alberto-rota/Ender3-Upgrade/Printables/LED Bar Holder.stl

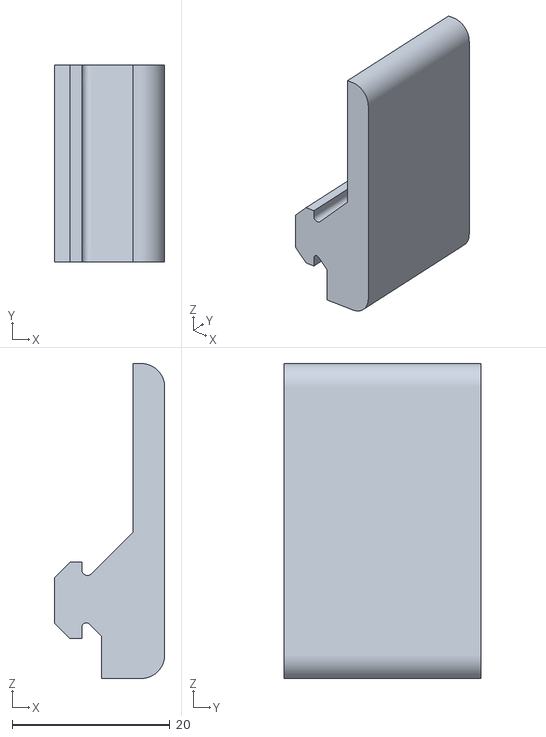
[picture p23: CAD file, 2023-01-06]
Printables/LED Bar Holder.stl
14.0 x 25.0 x 40.0
