alberto-rota/Ender3-Upgrade/Printables/Side_Drawers/Drawer_Bottom.stl

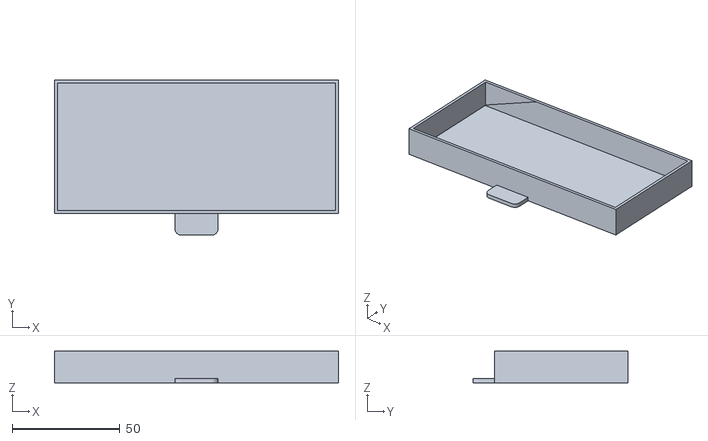
[picture p24: CAD file, 2023-03-15]
Printables/Side_Drawers/Drawer_Bottom.stl
131.5 x 72.0 x 14.8
