alberto-rota/Ender3-Upgrade/CAD/ExtrusionRail_20.dxf

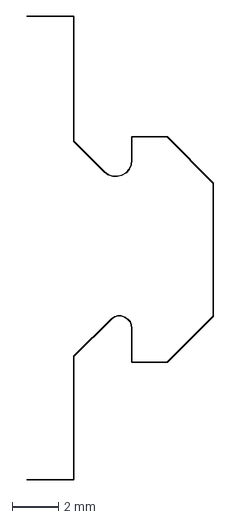
[picture p25: CAD file, 2023-01-06]
CAD/ExtrusionRail_20.dxf
8.05 x 20.0 mm
