alberto-rota/Ender3-Upgrade/CAD/LM2596 DC to DC Buck Converter 3 A/smd220uF.SLDPRT

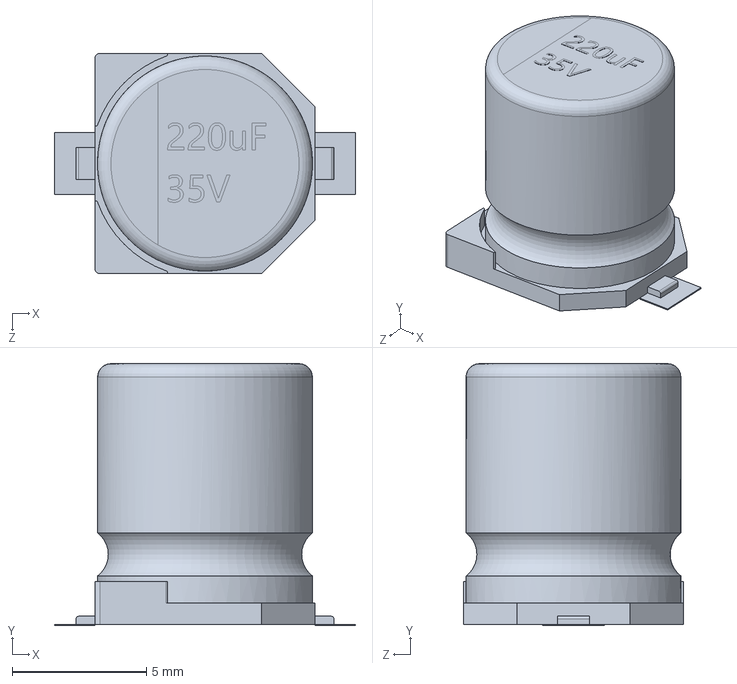
[picture p26: CAD file, 2023-01-05]
CAD/LM2596 DC to DC Buck Converter 3 A/smd220uF.SLDPRT
11.2 x 9.76 x 8.20 mm
