alberto-rota/Ender3-Upgrade/PCB/BuckConverter.dxf

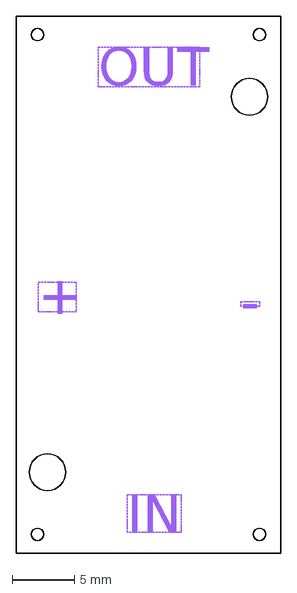
[picture p27: CAD file, 2023-01-05]
PCB/BuckConverter.dxf
IN
OUT
-
+
