alberto-rota/Ender3-Upgrade/Printables/Cablechain/cableChain_bedCorner_v2.stl

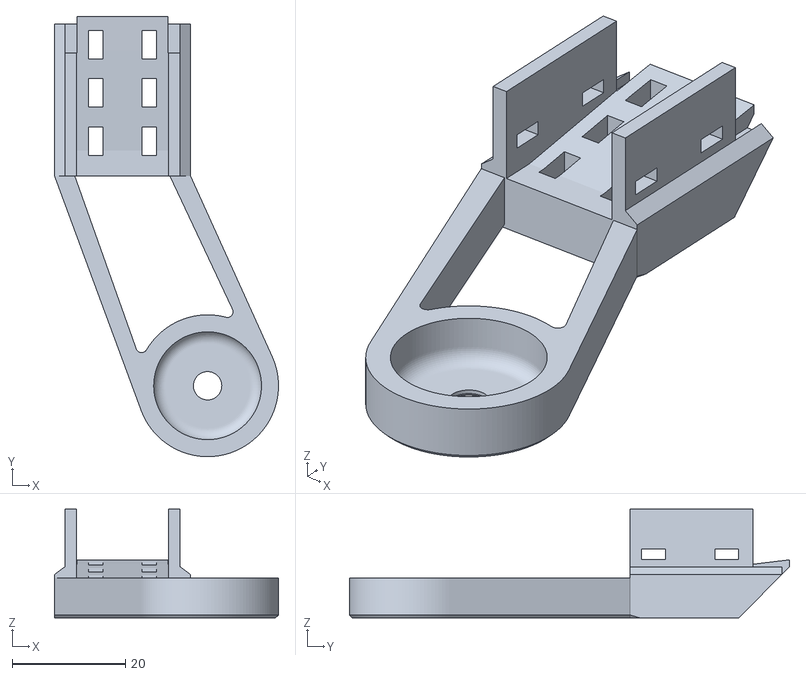
[picture p28: CAD file, 2023-03-15]
Printables/Cablechain/cableChain_bedCorner_v2.stl
39.5 x 77.6 x 19.2
