alberto-rota/Ender3-Upgrade/Printables/Camera Wire Clip.stl

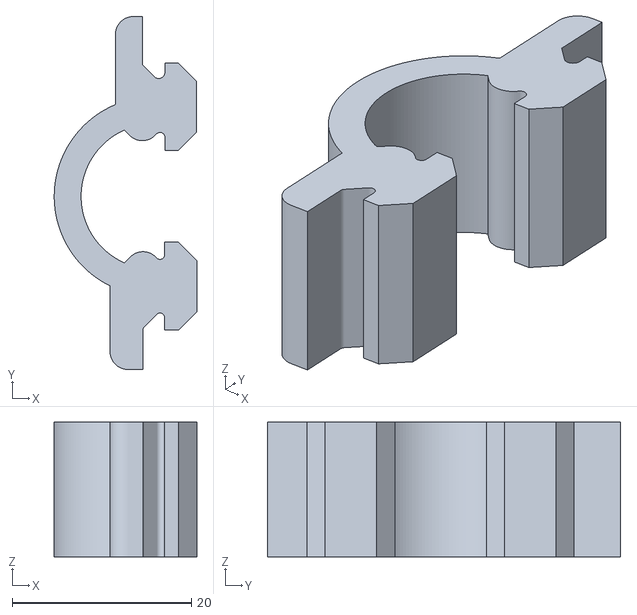
[picture p29: CAD file, 2023-01-06]
Printables/Camera Wire Clip.stl
15.9 x 39.4 x 15.0
