alberto-rota/Ender3-Upgrade/Printables/Front_Drawers/BOTTOM_DRAWER.stl

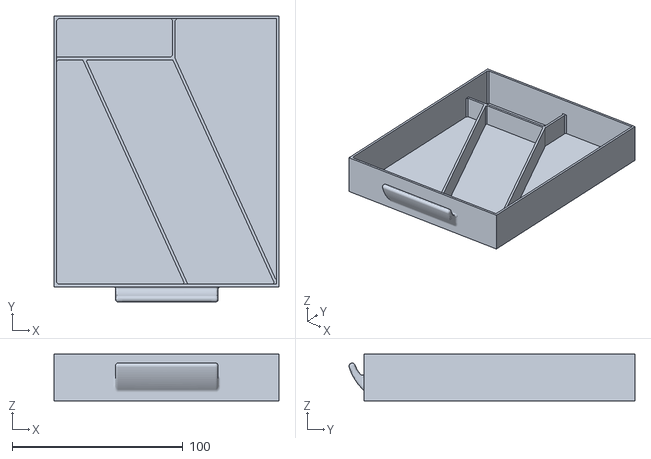
[picture p30: CAD file, 2023-03-15]
Printables/Front_Drawers/BOTTOM_DRAWER.stl
131.6 x 167.3 x 27.4
