alberto-rota/Ender3-Upgrade/Printables/Side_Drawers/Drawer_TopRight.stl

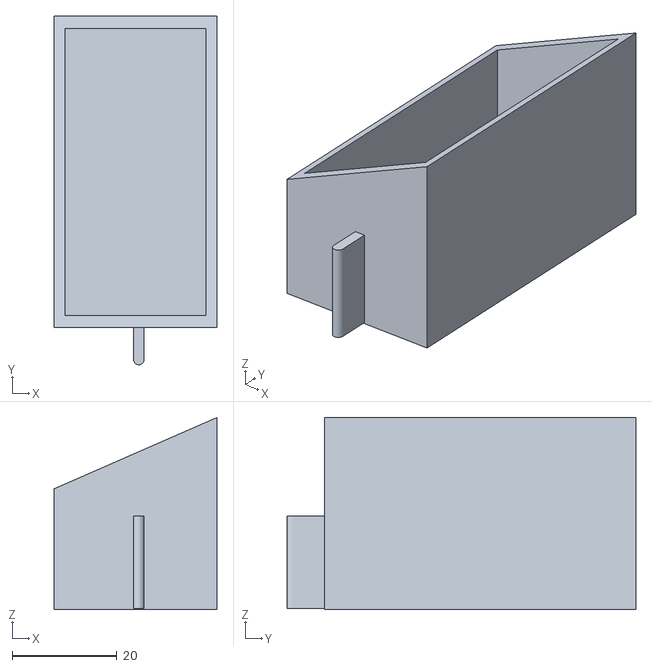
[picture p31: CAD file, 2023-03-15]
Printables/Side_Drawers/Drawer_TopRight.stl
31.0 x 66.4 x 36.6
