alberto-rota/Ender3-Upgrade/Printables/Cablechain/cableChain_40MountTop_v2.stl

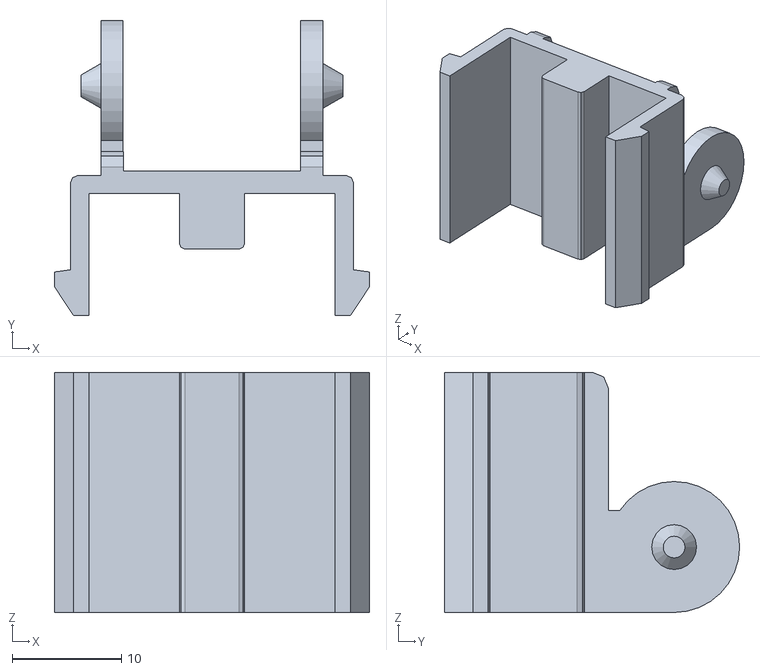
[picture p32: CAD file, 2023-03-15]
Printables/Cablechain/cableChain_40MountTop_v2.stl
28.9 x 27.1 x 22.0
