alberto-rota/Ender3-Upgrade/Printables/Side_Drawers/Drawer_Middle.stl

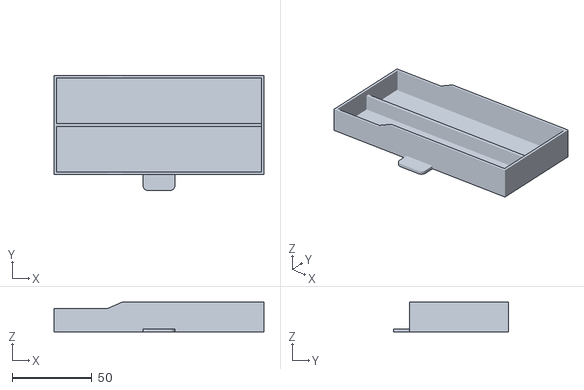
[picture p33: CAD file, 2023-03-15]
Printables/Side_Drawers/Drawer_Middle.stl
131.5 x 72.0 x 18.8
