alberto-rota/Ender3-Upgrade/CAD/LM2596 DC to DC Buck Converter 3 A/LM2596S.SLDPRT

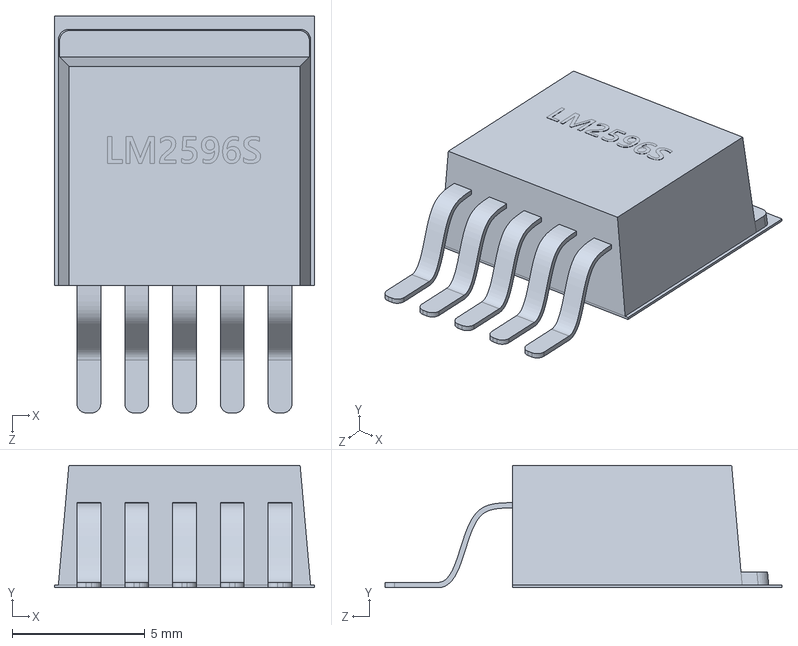
[picture p34: CAD file, 2023-01-05]
CAD/LM2596 DC to DC Buck Converter 3 A/LM2596S.SLDPRT
9.80 x 4.61 x 14.9 mm
