alberto-rota/Ender3-Upgrade/Printables/Cablechain/cableChain_Xend.stl

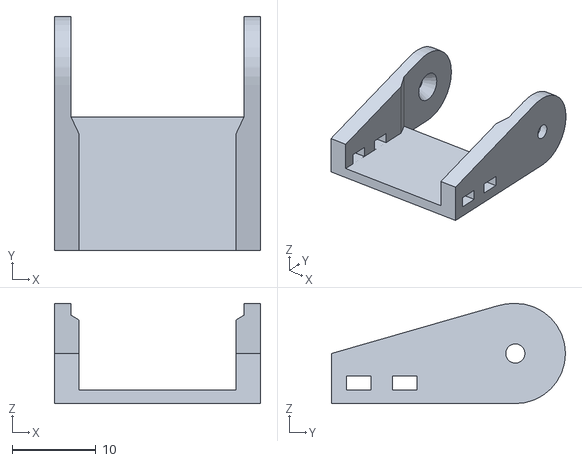
[picture p35: CAD file, 2023-03-15]
Printables/Cablechain/cableChain_Xend.stl
24.7 x 28.0 x 12.0
