alberto-rota/Ender3-Upgrade/Printables/Side_Drawers/Drawer_Holder.stl

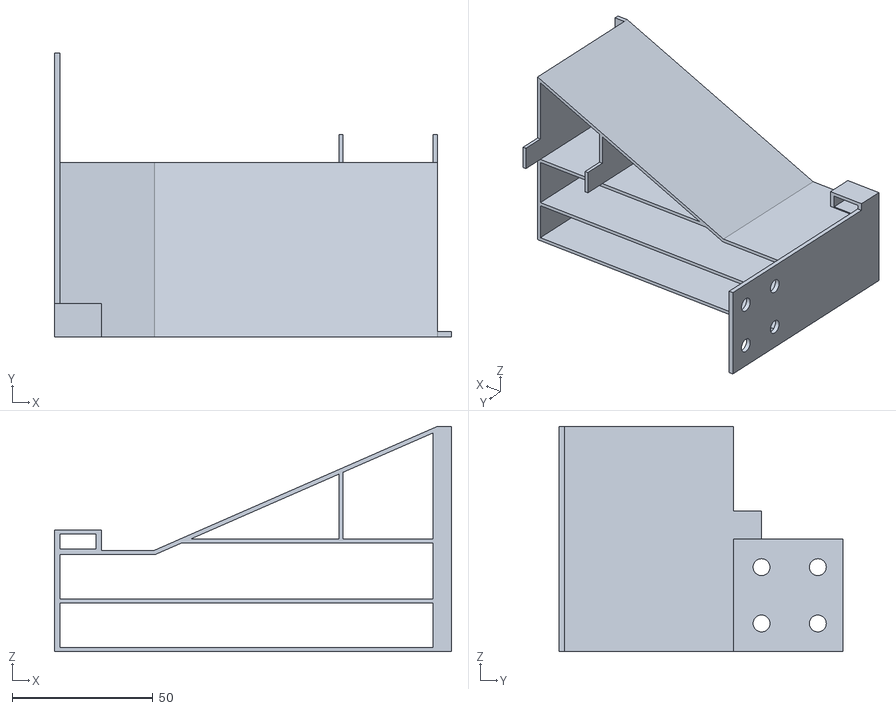
[picture p36: CAD file, 2023-03-15]
Printables/Side_Drawers/Drawer_Holder.stl
141.0 x 101.0 x 80.0
