alberto-rota/Ender3-Upgrade/CAD/LM2596 DC to DC Buck Converter 3 A/smbInductor470.SLDPRT

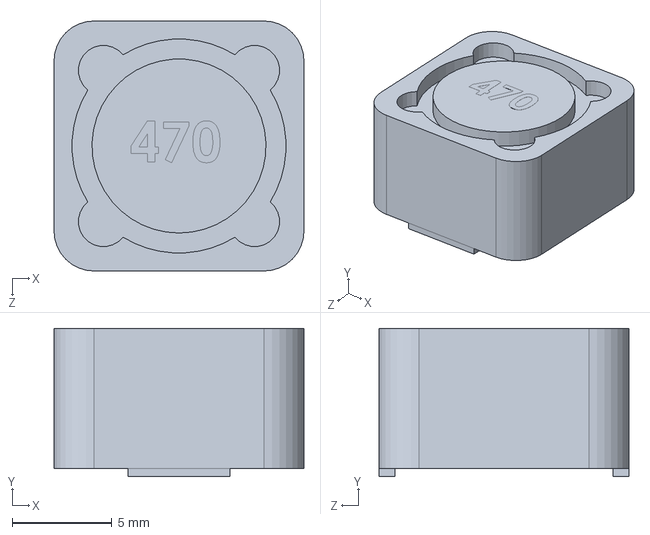
[picture p37: CAD file, 2023-01-05]
CAD/LM2596 DC to DC Buck Converter 3 A/smbInductor470.SLDPRT
12.5 x 7.41 x 12.5 mm
