alberto-rota/Ender3-Upgrade/CAD/LM2596 DC to DC Buck Converter 3 A/smdLED.SLDPRT

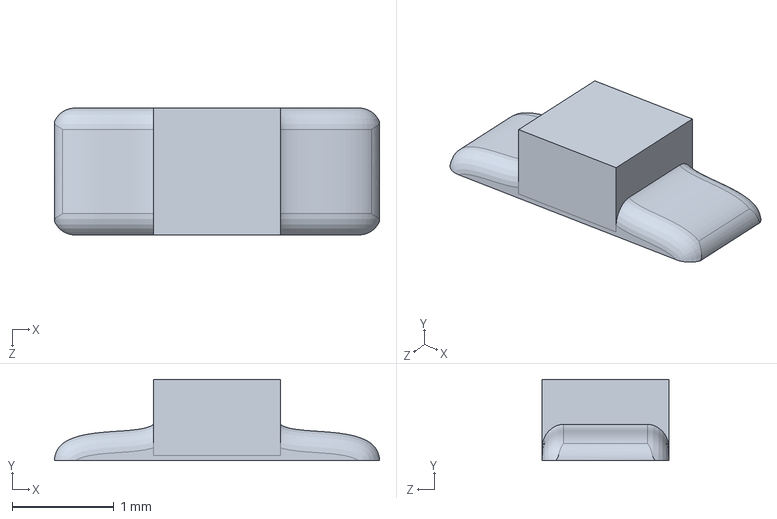
[picture p38: CAD file, 2023-01-05]
CAD/LM2596 DC to DC Buck Converter 3 A/smdLED.SLDPRT
3.20 x 0.8 x 1.25 mm
