alberto-rota/Ender3-Upgrade/Printables/Cablechain/cableChain_bedCornerCover_v2.stl

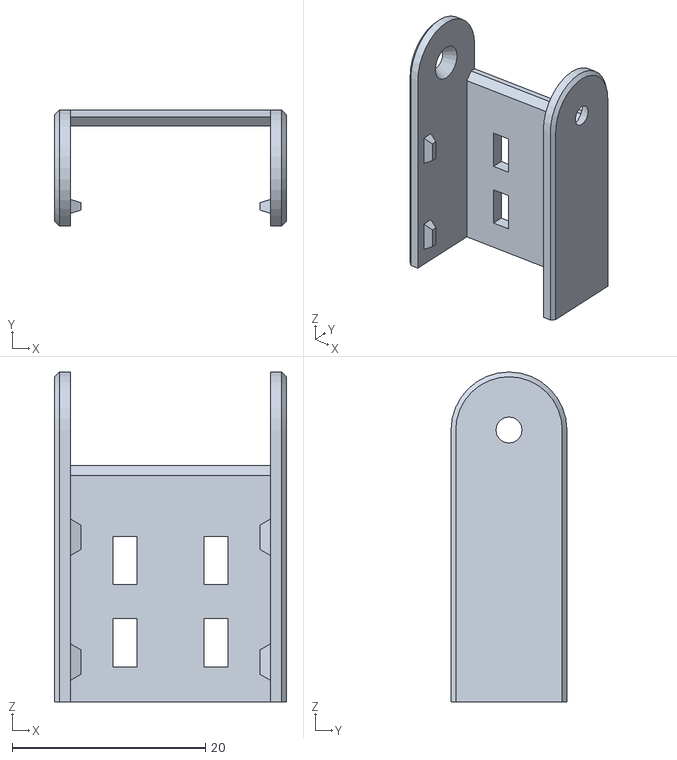
[picture p39: CAD file, 2023-03-15]
Printables/Cablechain/cableChain_bedCornerCover_v2.stl
24.0 x 12.0 x 34.1
