alberto-rota/Ender3-Upgrade/CAD/LM2596 DC to DC Buck Converter 3 A/TrimmerW203.SLDPRT

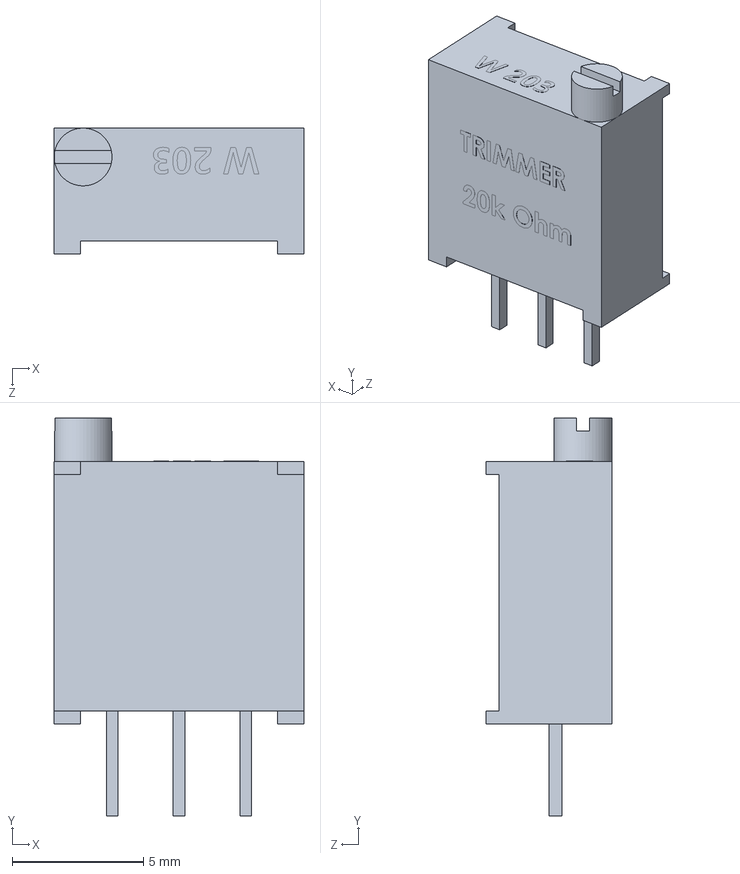
[picture p40: CAD file, 2023-01-05]
CAD/LM2596 DC to DC Buck Converter 3 A/TrimmerW203.SLDPRT
9.50 x 15.1 x 4.81 mm
