alberto-rota/Ender3-Upgrade/Printables/Cablechain/cableChain_link_v3.stl

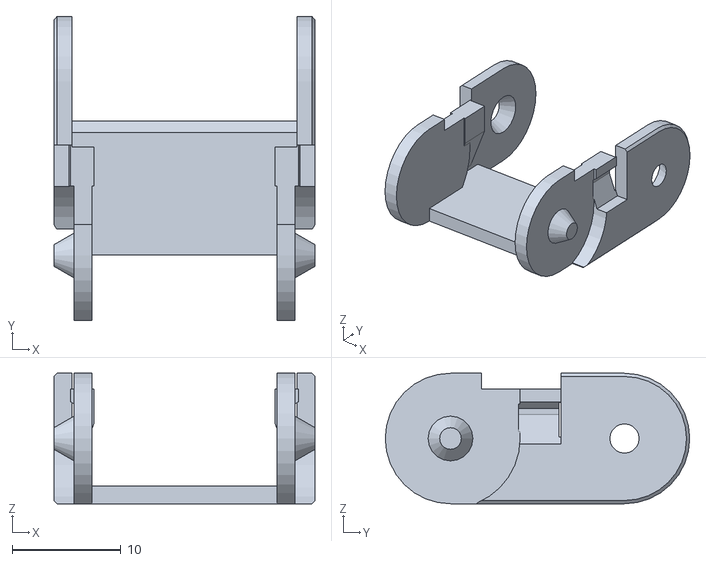
[picture p41: CAD file, 2023-03-15]
Printables/Cablechain/cableChain_link_v3.stl
24.0 x 28.0 x 12.0
