alberto-rota/Ender3-Upgrade/CAD/LM2596 DC to DC Buck Converter 3 A/lm2596board.SLDPRT

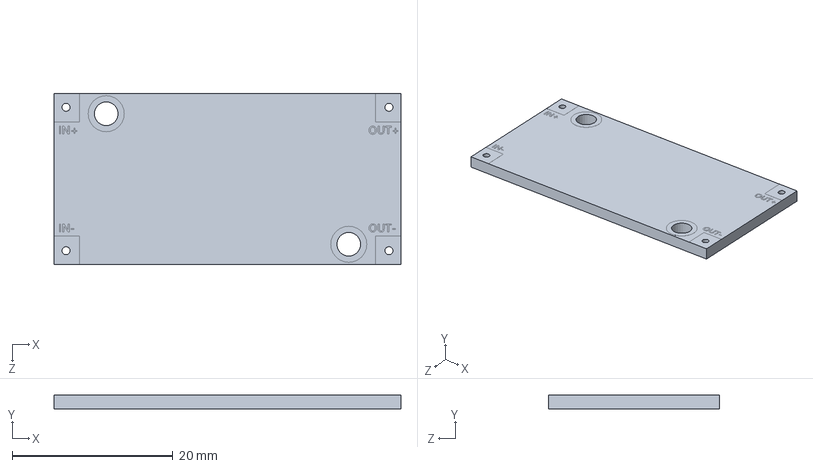
[picture p42: CAD file, 2023-01-05]
CAD/LM2596 DC to DC Buck Converter 3 A/lm2596board.SLDPRT
43.2 x 1.71 x 21.2 mm
