alberto-rota/Ender3-Upgrade/Printables/Cablechain/cableChain_XendCover.stl

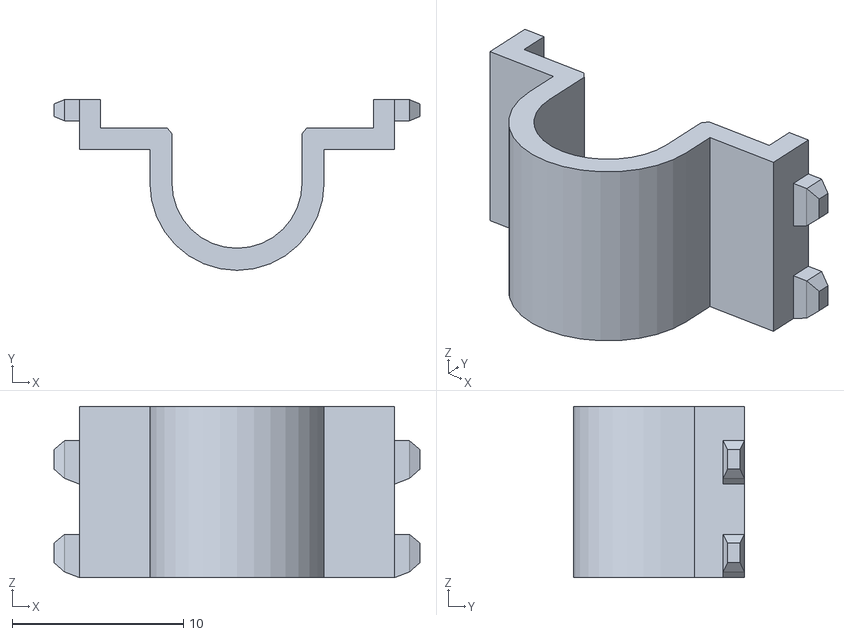
[picture p43: CAD file, 2023-03-15]
Printables/Cablechain/cableChain_XendCover.stl
21.4 x 9.98 x 10.0
