alberto-rota/Ender3-Upgrade/Printables/Cablechain/cableChain_40MountTop.stl

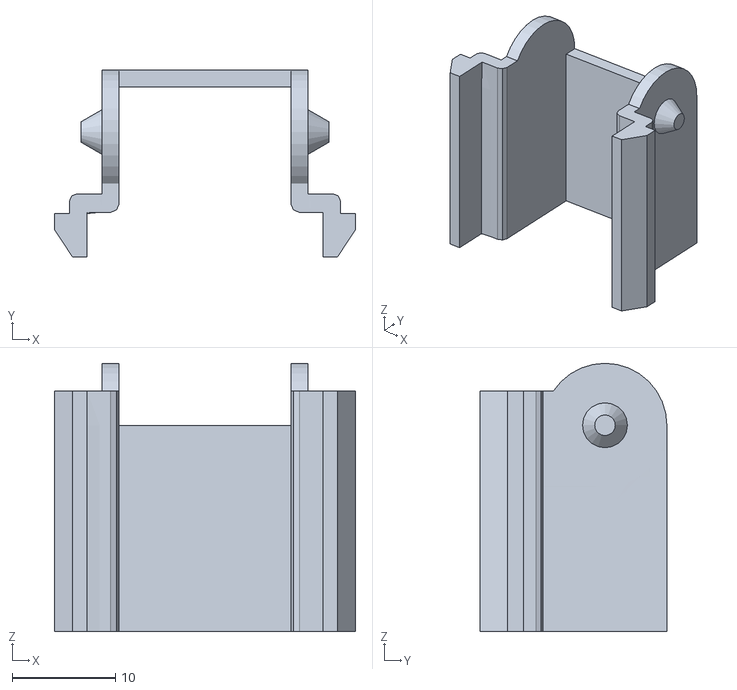
[picture p44: CAD file, 2023-03-15]
Printables/Cablechain/cableChain_40MountTop.stl
29.2 x 18.1 x 26.0
