alberto-rota/Ender3-Upgrade/Printables/Cablechain/cableChain_linkCover_v2.stl

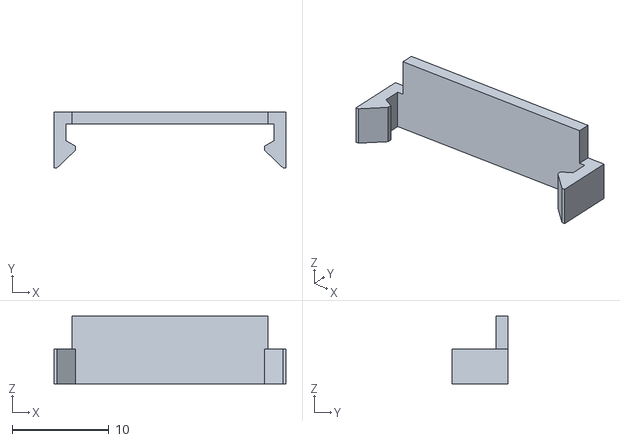
[picture p45: CAD file, 2023-03-15]
Printables/Cablechain/cableChain_linkCover_v2.stl
24.0 x 5.80 x 7.00
