alberto-rota/Ender3-Upgrade/Printables/Cablechain/cableChain_bedCorner.stl

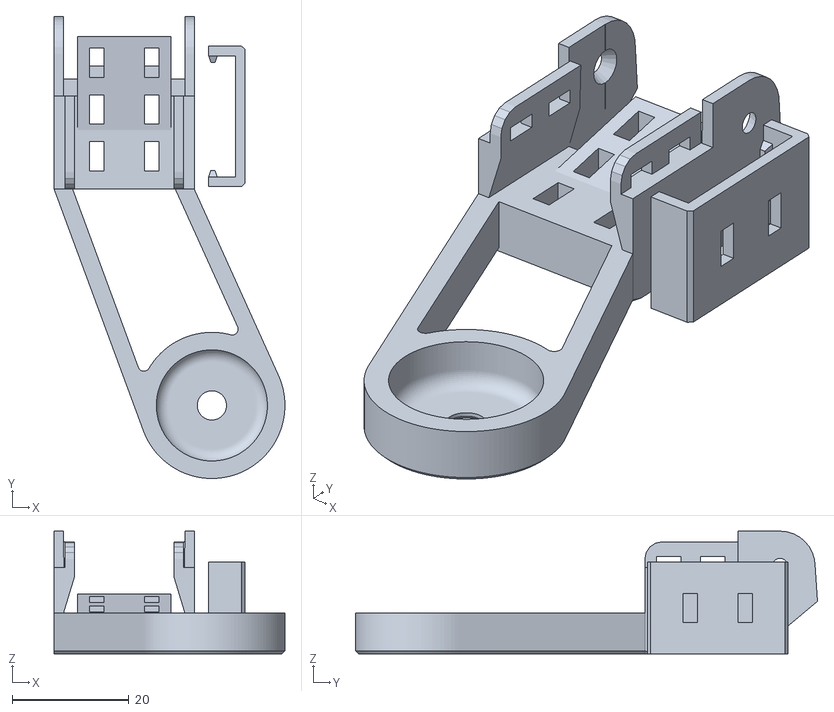
[picture p46: CAD file, 2023-03-15]
Printables/Cablechain/cableChain_bedCorner.stl
39.5 x 79.0 x 21.0
