alberto-rota/Ender3-Upgrade/CAD/LM2596 DC to DC Buck Converter 3 A/smdS537diode.SLDPRT

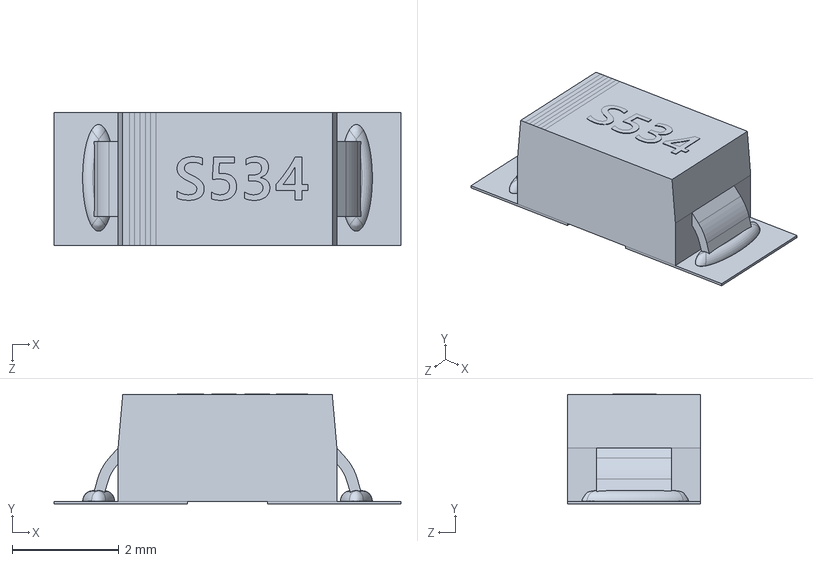
[picture p47: CAD file, 2023-01-05]
CAD/LM2596 DC to DC Buck Converter 3 A/smdS537diode.SLDPRT
6.50 x 2.06 x 2.50 mm
