alberto-rota/Ender3-Upgrade/Printables/Cablechain/cableChain_plateMount_v2.stl

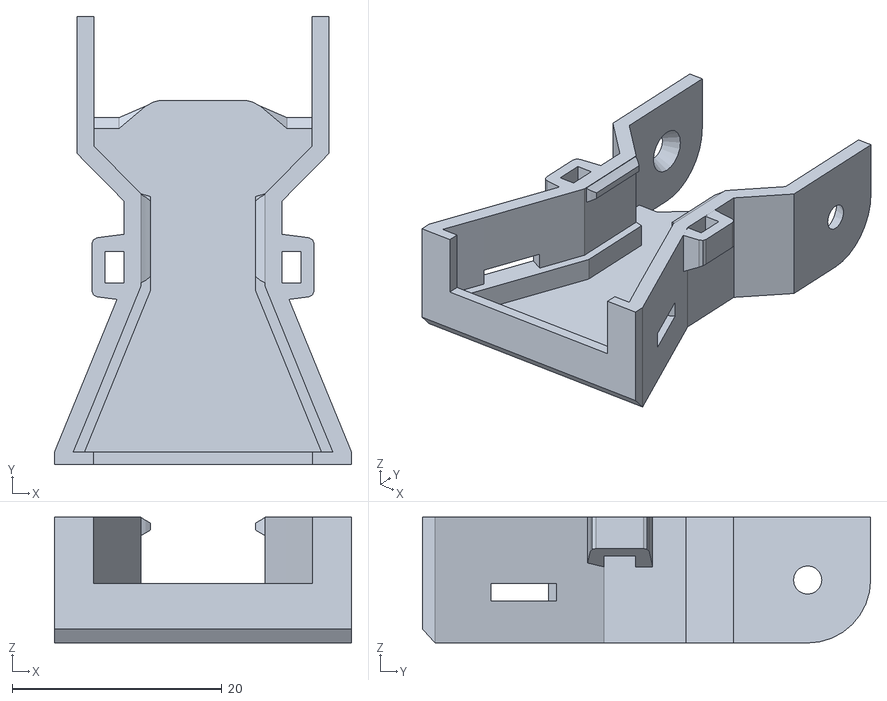
[picture p48: CAD file, 2023-03-15]
Printables/Cablechain/cableChain_plateMount_v2.stl
28.3 x 42.7 x 12.0
