alberto-rota/Ender3-Upgrade/CAD/LM2596 DC to DC Buck Converter 3 A/smdceramiccapacitor.SLDPRT

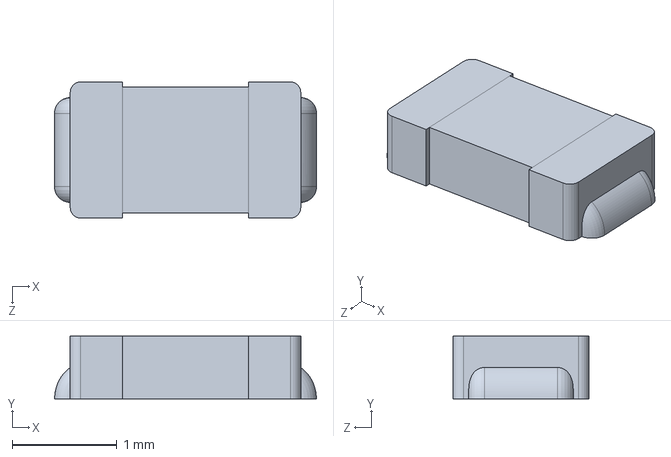
[picture p49: CAD file, 2023-01-05]
CAD/LM2596 DC to DC Buck Converter 3 A/smdceramiccapacitor.SLDPRT
2.50 x 0.6 x 1.30 mm
